A0Cybernetics/C.A.T/Documents/buildGuidePictures/mouseProperties.png

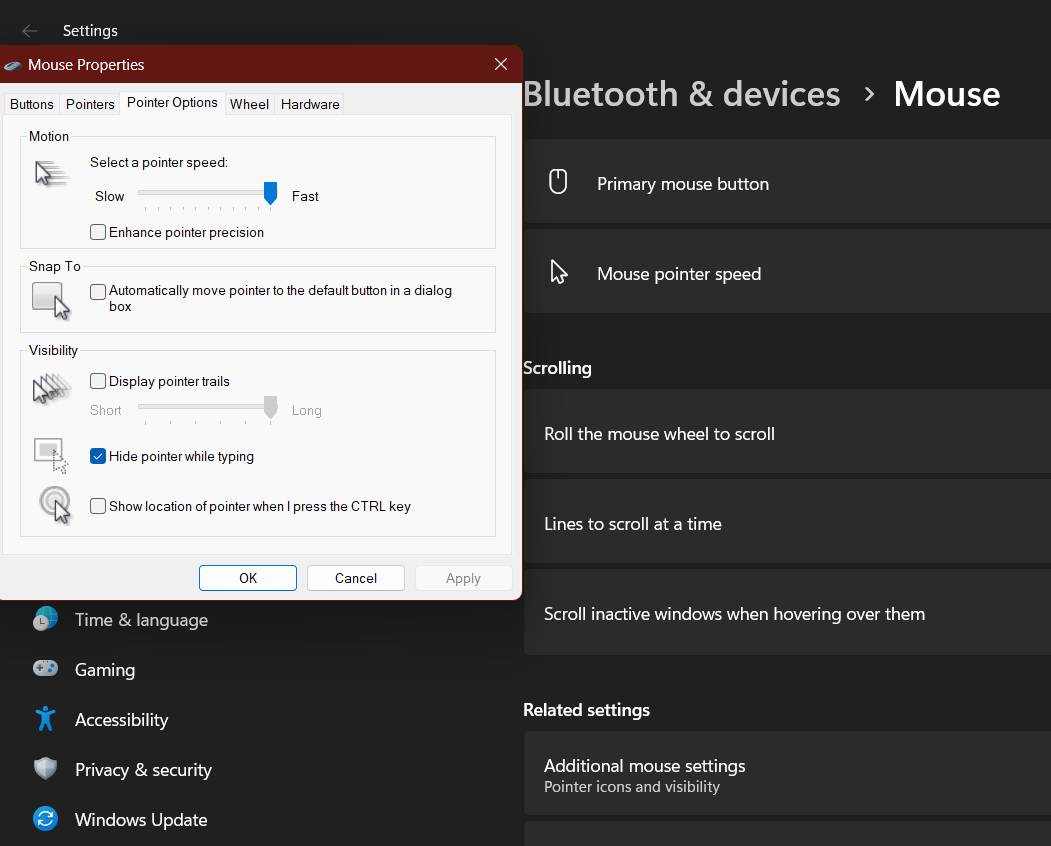
Documents/buildGuidePictures/mouseProperties.png
