A0Cybernetics/C.A.T/Documents/buildGuidePictures/VL53L1X.jpg

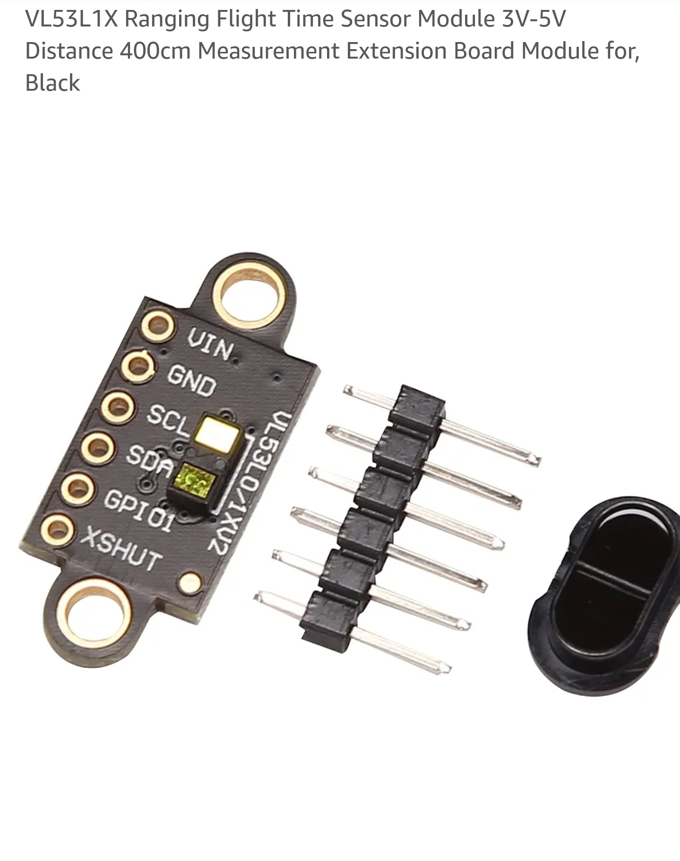
Documents/buildGuidePictures/VL53L1X.jpg
